grigoriev-vladimir/R1C4-Autonomous-Tracking-Robot/hardware/3d_models/R1-C4 - Equerre arret translation bas.step

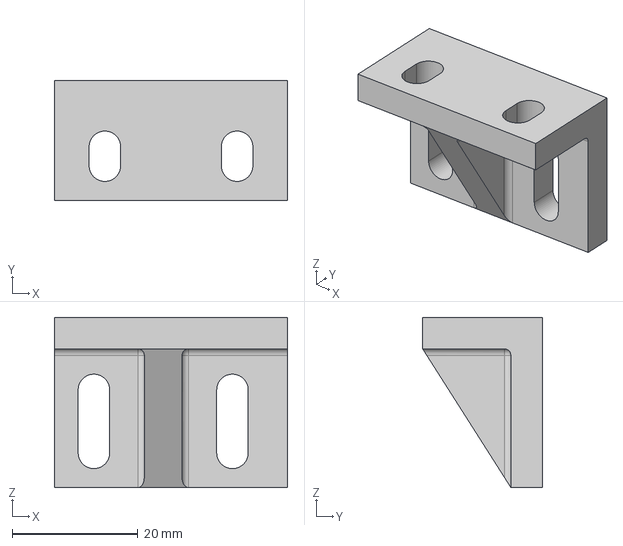
[picture p15: CAD file, 2026-05-31]
hardware/3d_models/R1-C4 - Equerre arret translation bas.step
37.0 x 19.0 x 27.0 mm
