grigoriev-vladimir/R1C4-Autonomous-Tracking-Robot/hardware/3d_models/R1C4-translation_stop.step

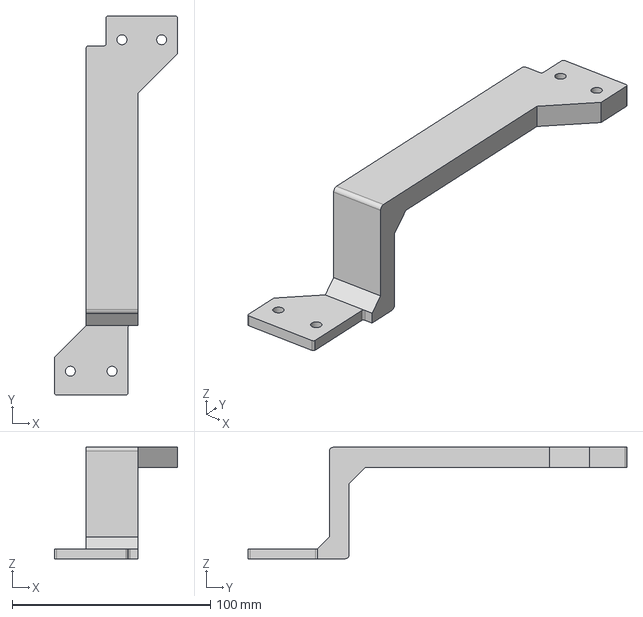
[picture p16: CAD file, 2026-05-31]
hardware/3d_models/R1C4-translation_stop.step
62.0 x 191.0 x 56.2 mm
