grigoriev-vladimir/R1C4-Autonomous-Tracking-Robot/hardware/3d_models/R1-C4 - Equerre support moteur.step

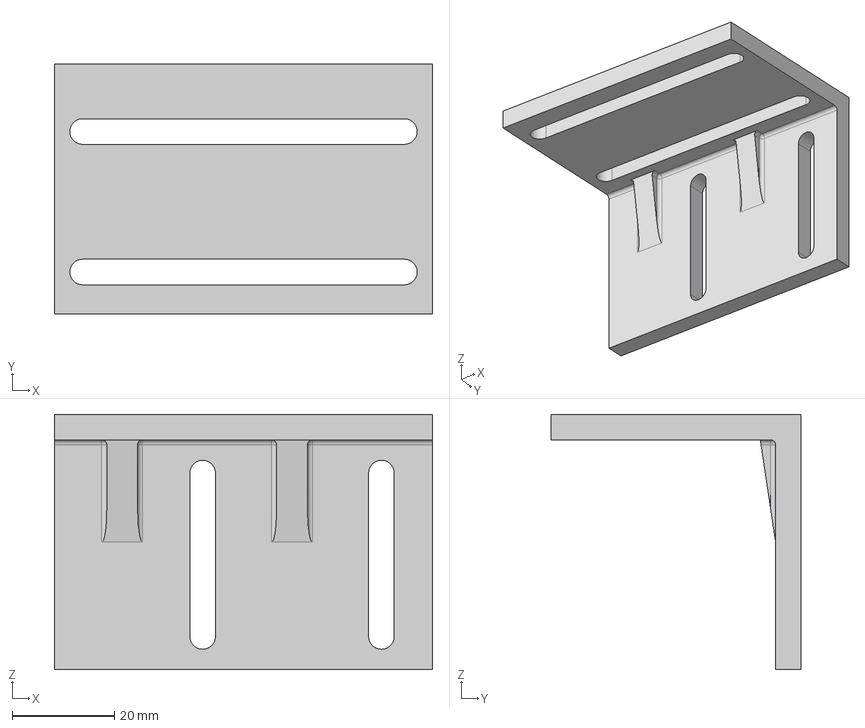
[picture p17: CAD file, 2026-05-31]
hardware/3d_models/R1-C4 - Equerre support moteur.step
74.0 x 49.0 x 50.0 mm
