grigoriev-vladimir/R1C4-Autonomous-Tracking-Robot/hardware/3d_models/R1-C4 - Equerre arret translation haut.step

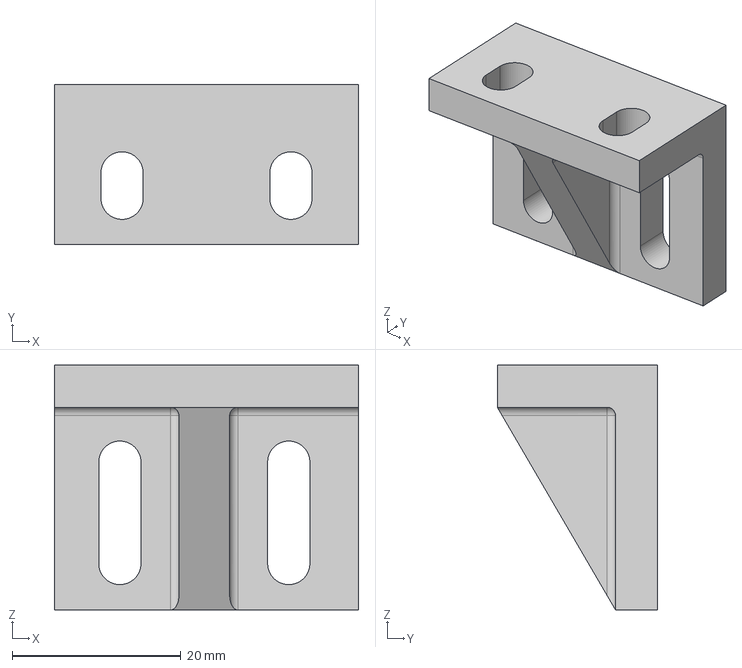
[picture p18: CAD file, 2026-05-31]
hardware/3d_models/R1-C4 - Equerre arret translation haut.step
36.0 x 19.0 x 29.0 mm
