grigoriev-vladimir/R1C4-Autonomous-Tracking-Robot/hardware/3d_models/R1-C4 - Leg.step

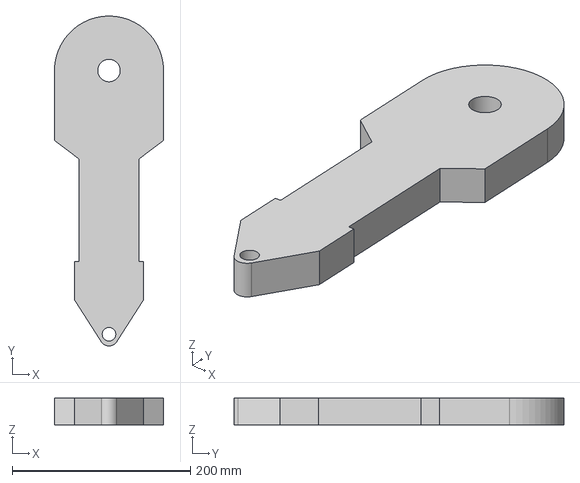
[picture p19: CAD file, 2026-05-31]
hardware/3d_models/R1-C4 - Leg.step
122.3 x 369.8 x 30.0 mm
