grigoriev-vladimir/R1C4-Autonomous-Tracking-Robot/hardware/3d_models/R1-C4 - Axe guide en translation.step

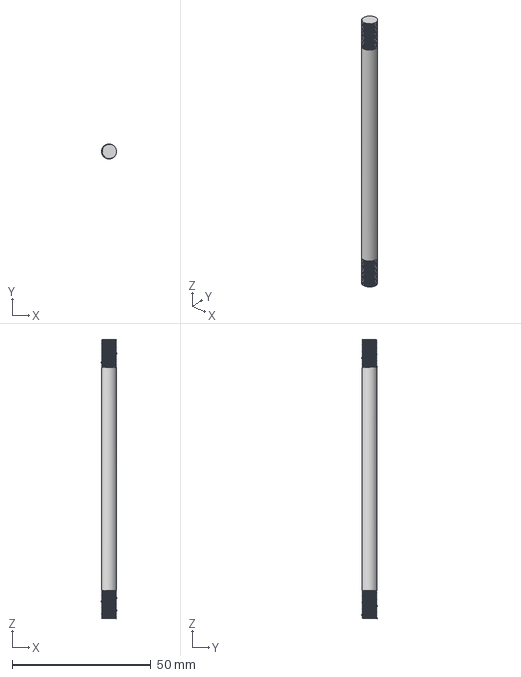
[picture p20: CAD file, 2026-05-31]
hardware/3d_models/R1-C4 - Axe guide en translation.step
5.44 x 5.44 x 100.4 mm
