grigoriev-vladimir/R1C4-Autonomous-Tracking-Robot/hardware/3d_models/R1C4-right_wheel.step

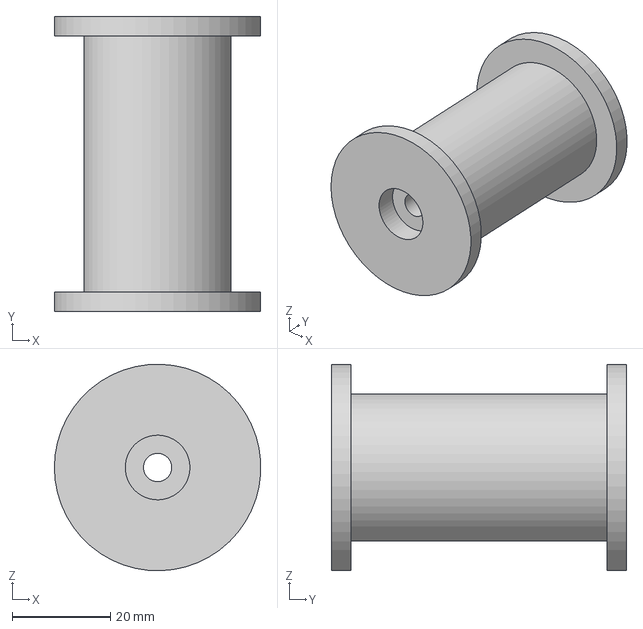
[picture p21: CAD file, 2026-05-31]
hardware/3d_models/R1C4-right_wheel.step
42.0 x 60.0 x 42.0 mm
