grigoriev-vladimir/R1C4-Autonomous-Tracking-Robot/hardware/3d_models/R1-C4 - Cage d'ascenseur V2.step

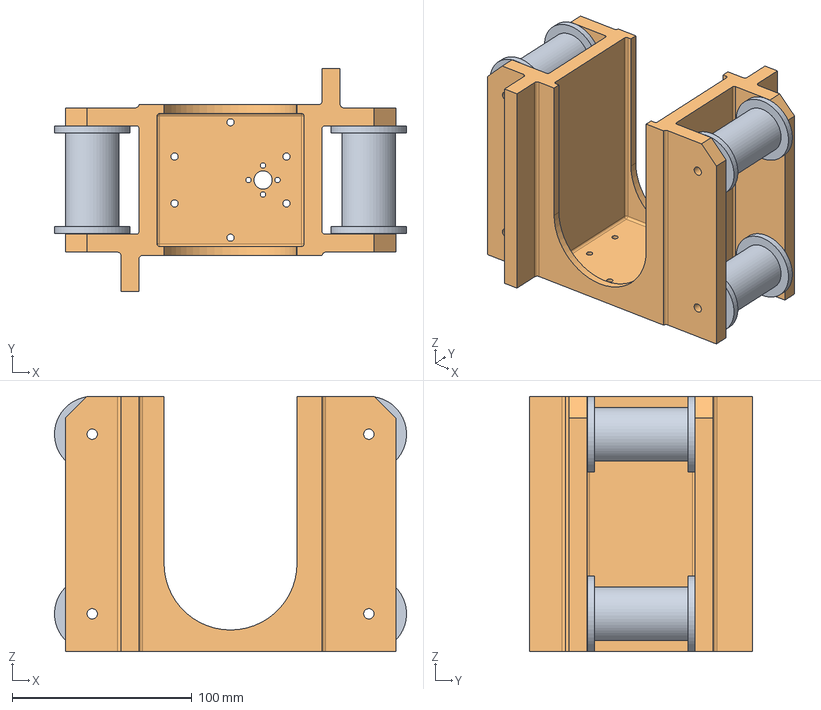
[picture p22: CAD file, 2026-05-31]
hardware/3d_models/R1-C4 - Cage d'ascenseur V2.step
196.0 x 124.4 x 142.0 mm
