grigoriev-vladimir/R1C4-Autonomous-Tracking-Robot/hardware/3d_models/R1-C4 - Axe center foot.step

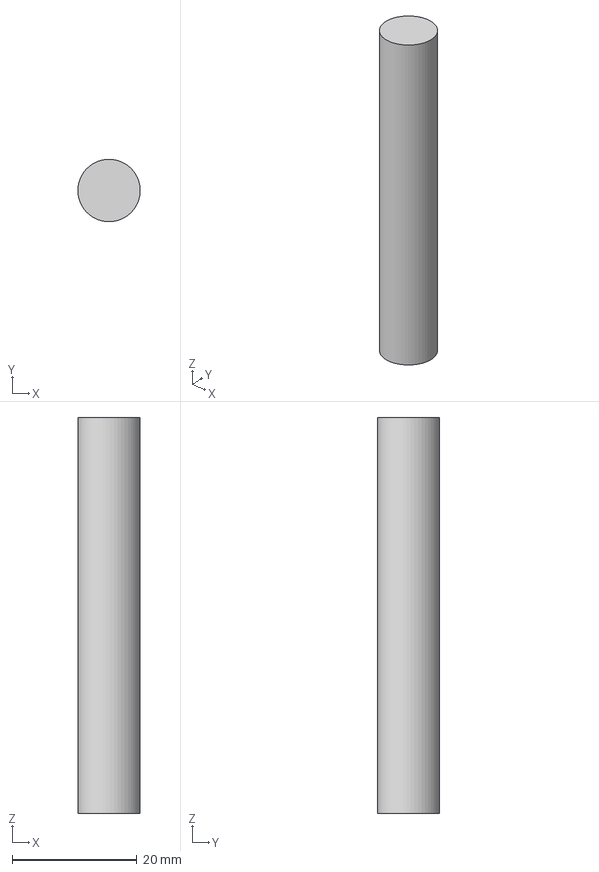
[picture p23: CAD file, 2026-05-31]
hardware/3d_models/R1-C4 - Axe center foot.step
10.00 x 10.0 x 63.5 mm
