grigoriev-vladimir/R1C4-Autonomous-Tracking-Robot/hardware/3d_models/R1-C4 - Ankle.step

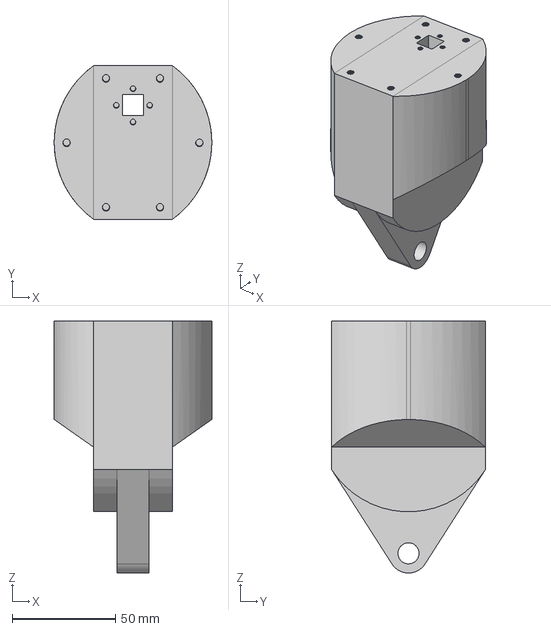
[picture p24: CAD file, 2026-05-31]
hardware/3d_models/R1-C4 - Ankle.step
76.2 x 74.3 x 121.8 mm
